rh1tech/protea32/3D/W25Q128JVSIQ.stp

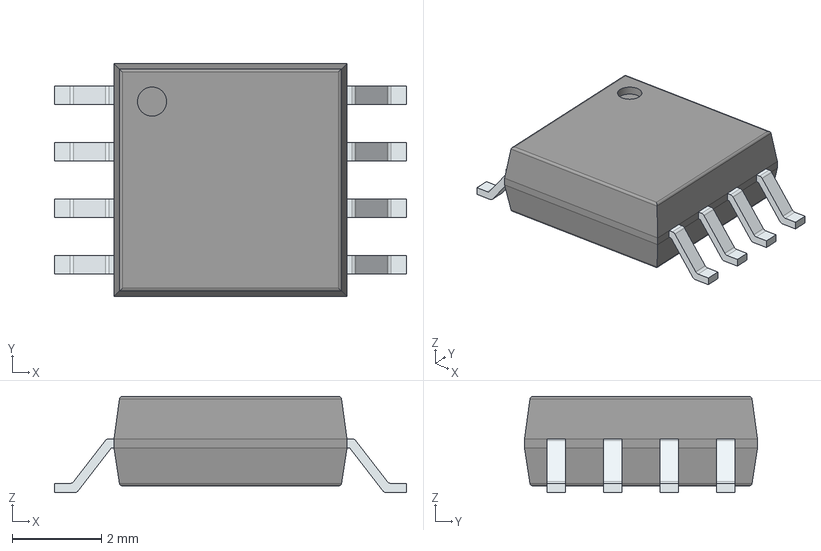
[picture p16: CAD file, 2025-10-18]
3D/W25Q128JVSIQ.stp
7.90 x 5.23 x 2.16 mm
PinsArrayLR
