rh1tech/protea32/3D/DS05-127-2-03BK-SMT-TR.step

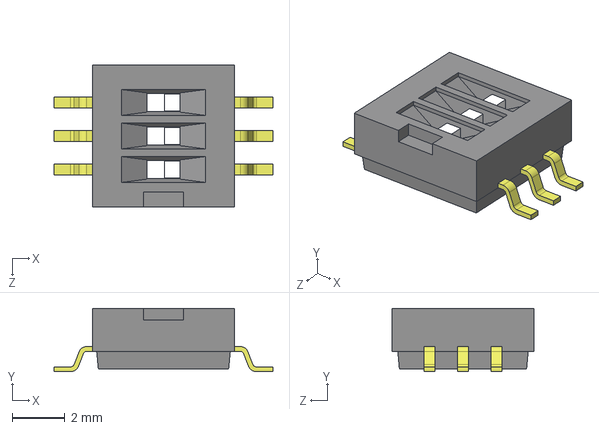
[picture p18: CAD file, 2025-10-18]
3D/DS05-127-2-03BK-SMT-TR.step
8.30 x 2.40 x 5.38 mm
