rh1tech/protea32/3D/1TS003B.step

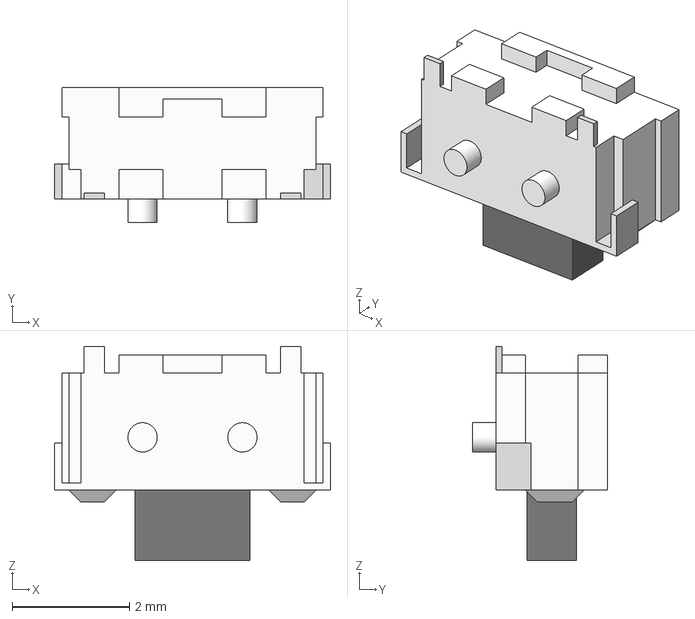
[picture p19: CAD file, 2025-10-18]
3D/1TS003B.step
4.70 x 2.30 x 3.65 mm
