rh1tech/protea32/3D/PJ320D.STEP

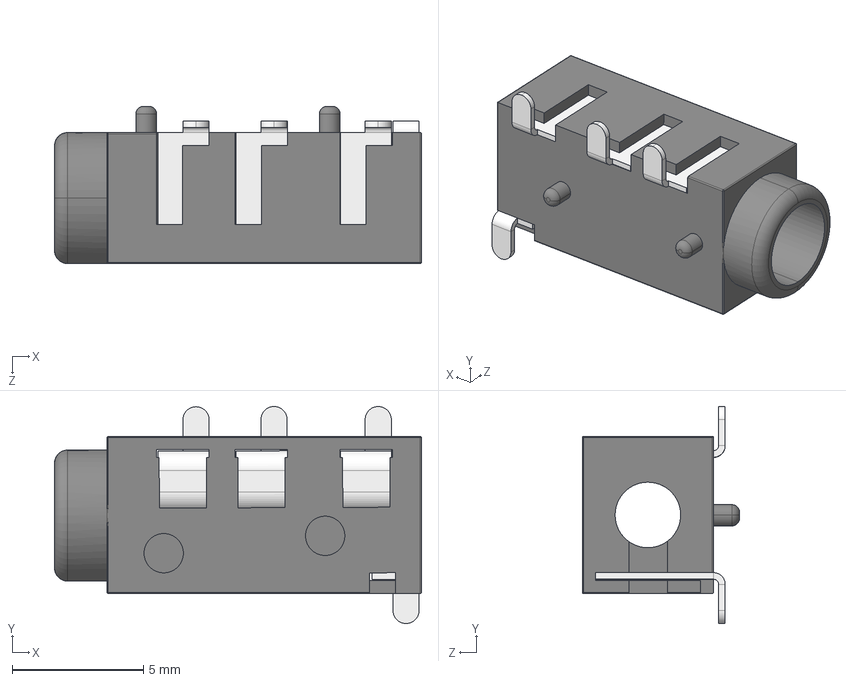
[picture p20: CAD file, 2025-10-18]
3D/PJ320D.STEP
14.0 x 8.28 x 6.00 mm
PJ320A
PJ320D-Pin x 3
PJ320D-Pin-B
