rh1tech/protea32/3D/DSUB-9_Female_Horizontal_P2.77x2.84mm_EdgePinOffset9.90mm_Housed_MountingHolesOffset11.32mm.step

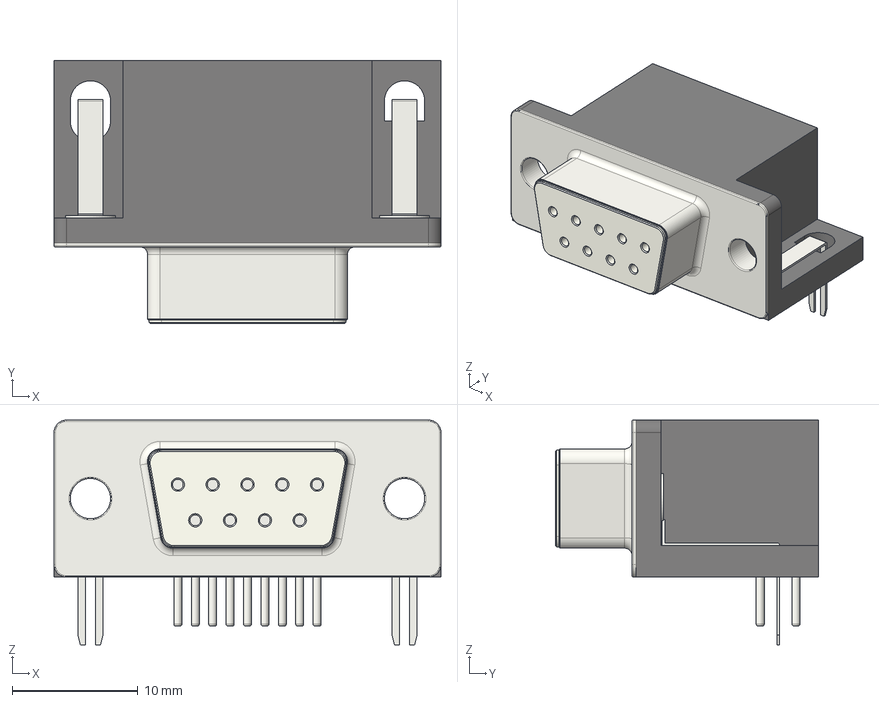
[picture p21: CAD file, 2025-10-18]
3D/DSUB-9_Female_Horizontal_P2.77x2.84mm_EdgePinOffset9.90mm_Housed_MountingHolesOffset11.32mm.step
30.8 x 20.9 x 17.9 mm
