rh1tech/protea32/3D/SO-8_5.3x6.2mm_P1.27mm.step

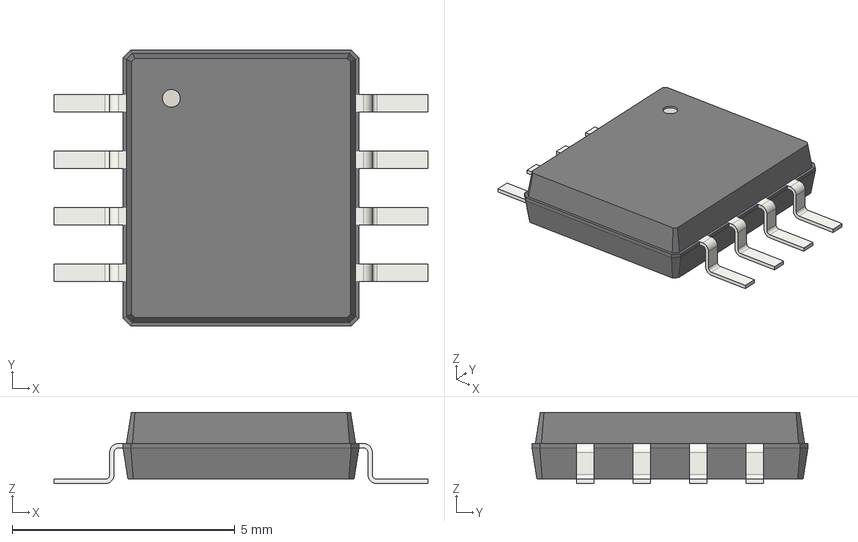
[picture p22: CAD file, 2025-10-18]
3D/SO-8_5.3x6.2mm_P1.27mm.step
8.40 x 6.20 x 1.60 mm
