rh1tech/protea32/3D/3225 SMD Crystal Oscillator.STEP

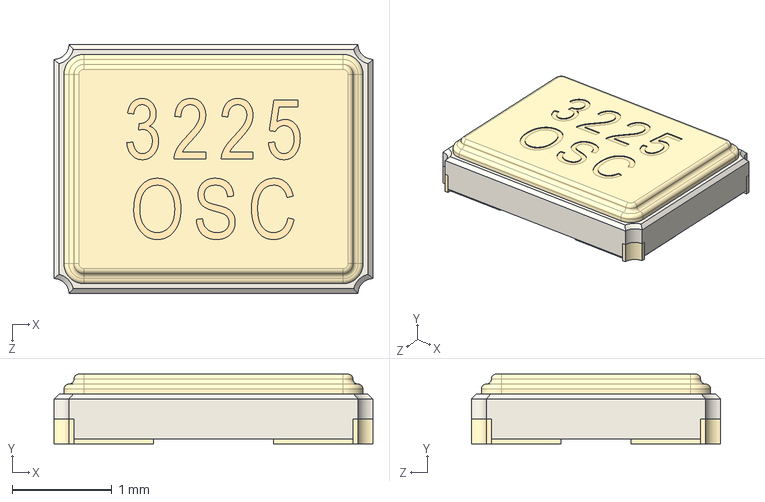
[picture p23: CAD file, 2025-10-18]
3D/3225 SMD Crystal Oscillator.STEP
3.20 x 0.7 x 2.50 mm
