rh1tech/protea32/3D/TS3USB221RSER.stp

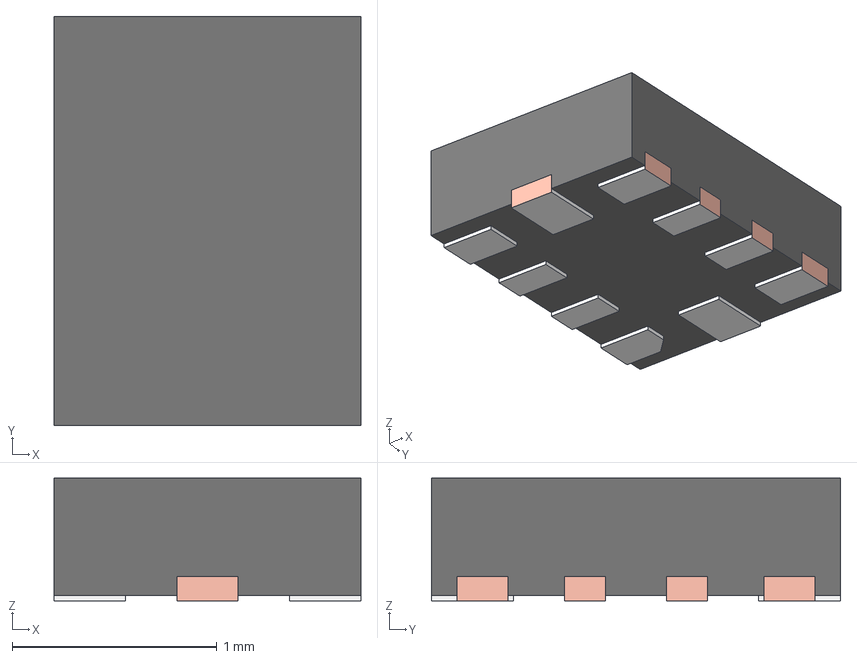
[picture p24: CAD file, 2025-10-18]
3D/TS3USB221RSER.stp
1.50 x 2.00 x 0.6 mm
FRAME-RSE0010A
BODY-QFN
PIN1-ID
