rh1tech/protea32/3D/HRO_TYPE-C-31-M-12.step

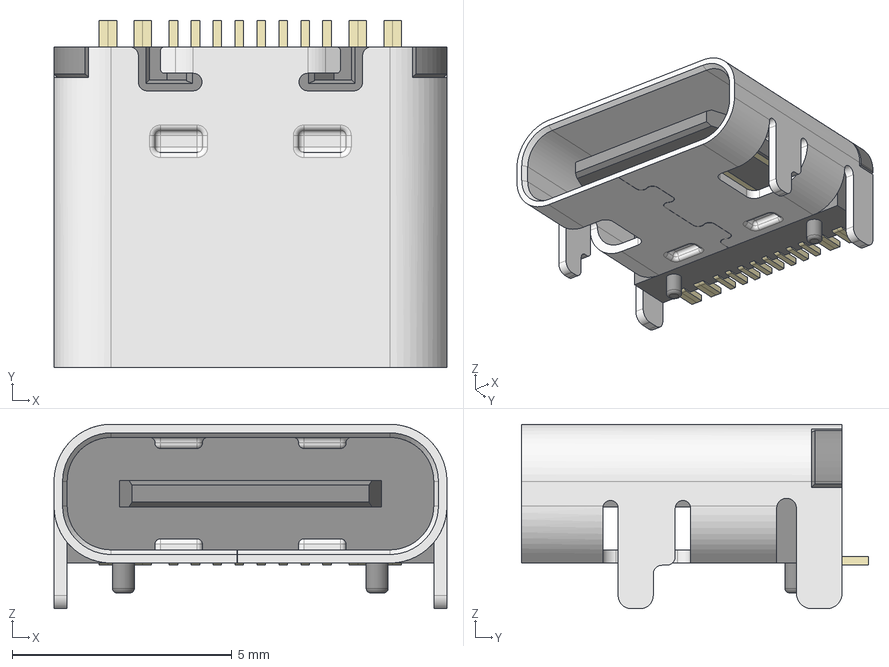
[picture p25: CAD file, 2025-10-18]
3D/HRO_TYPE-C-31-M-12.step
8.95 x 7.90 x 4.20 mm
