rh1tech/protea32/3D/USB1035-GF-P-0-B-B.stp

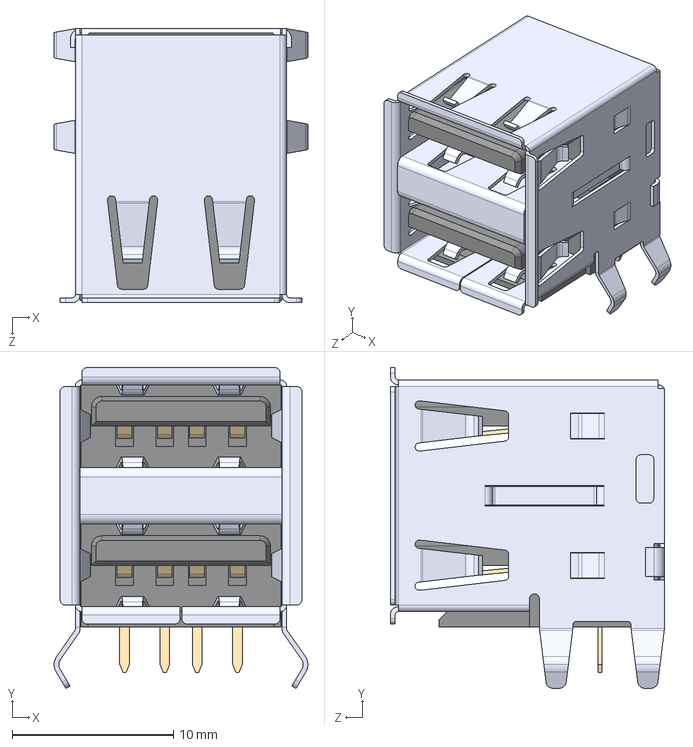
[picture p26: CAD file, 2025-10-18]
3D/USB1035-GF-P-0-B-B.stp
15.7 x 19.9 x 17.0 mm
