rh1tech/protea32/3D/CUI_DEVICES_RCJ-013.step

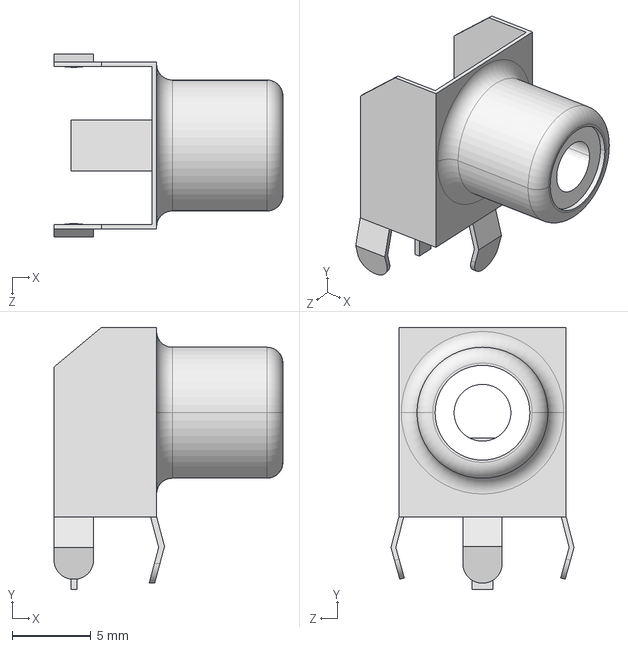
[picture p27: CAD file, 2025-10-18]
3D/CUI_DEVICES_RCJ-013.step
14.5 x 16.6 x 11.6 mm
