rh1tech/protea32/3D/SOP-16_3.9x9.9mm_P1.27mm.step

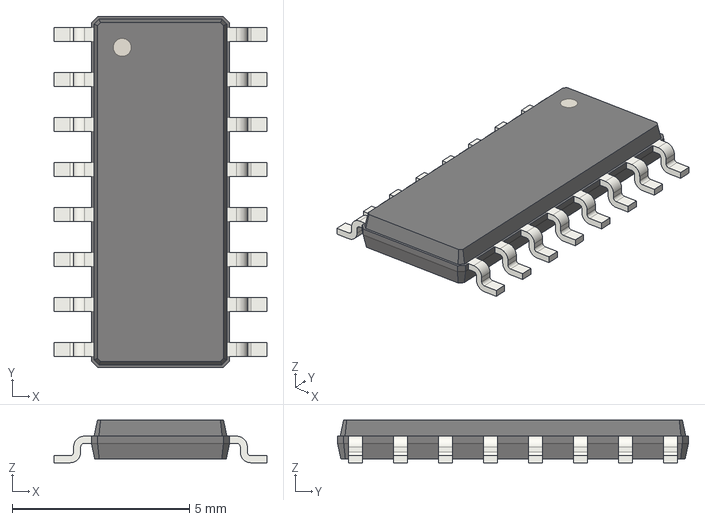
[picture p28: CAD file, 2025-10-18]
3D/SOP-16_3.9x9.9mm_P1.27mm.step
6.00 x 9.90 x 1.20 mm
